sakhnik/arduin-o-punch/arduino/src/Operation.cpp

#include "Operation.h"
#include "Buzzer.h"
#include "Settings.h"
#include "Bluetooth.h"
#include "Network.h"
#include "CpuFreq.h"
#include "defs.h"
#include "ActivityCounter.h"
#include "RtcLog.h"
#include <SPI.h>
#include <esp_sleep.h>
#include <driver/gpio.h>
#include <RTClib.h>
#include <Preferences.h>

// Should always keep non-DST time
RTC_DS3231 rtc;

namespace {

Preferences prefs;

// Hold some pins in the high state during sleep to keep RFC522 and DS3231 switched off and to avoid parasitic current
static constexpr const int HIGH_PINS[] = {MOSFET_PIN, BUZZER_PIN};

constexpr const int TIME_TO_SLEEP_MS = 500;

constexpr const char *const PREF_STATS = "stats";
constexpr const char *const PREF_PREV_TRANSITION = "prev-trans";
constexpr const char *const PREF_PREV_MODE = "prev-mode";
constexpr const char *const PREF_TIMES = "times";

} //namespace;

Operation::Operation(Buzzer &buzzer, Settings &settings, OutMux &outMux, Bluetooth &bluetooth, Network &network)
    : buzzer{buzzer}
    , settings{settings}
    , bluetooth{bluetooth}
    , network{network}
    , puncher{settings, *this, buzzer, outMux}
{
}

int Operation::Setup()
{
    gpio_deep_sleep_hold_dis();
    for (int pin : HIGH_PINS) {
        gpio_hold_dis(static_cast<gpio_num_t>(pin));
    }

    pinMode(MOSFET_PIN, OUTPUT);
    pinMode(WAKEUP_PIN, INPUT_PULLUP);

    // Power on the RFID reader
    digitalWrite(MOSFET_PIN, LOW);

    Wire.setPins(I2C_SDA, I2C_SCL);
    if (!rtc.begin()) {
        Serial.println("Couldn't find RTC");
        Serial.flush();
        buzzer.SignalRTCFail();
        return -1;
    }

    if (puncher.Setup())
        return -1;

    if (RtcLog::IsReliable()) {
        // Restore the previous mode to preserve the accurate statistics
        prefs.begin(PREF_STATS, true);
        prevTransitionTime = prefs.getULong(PREF_PREV_TRANSITION, rtc.now().unixtime());
        auto prevMode = prefs.getInt(PREF_PREV_MODE, static_cast<int>(Mode::Sleep));
        if (prevMode < static_cast<int>(Mode::Count)) {
            mode = static_cast<Mode>(prevMode);
        }
        prefs.getBytes(PREF_TIMES, timeStats.data(), sizeof(timeStats));
        prefs.end();
    } else {
        prevTransitionTime = rtc.now().unixtime();
    }

    prevCardTimeMs = millis();
    return 0;
}

void Operation::SetupLate()
{
    if (!settings.IsKeyDefault()) {
        // Set the CPU frequency to 10 MHz for power optimization
        setCpuFrequencyMhz(10);
        Serial.print(F("CPU Frequency: "));
        Serial.print(getCpuFrequencyMhz());
        Serial.println(F(" MHz"));

        // Transition to the default mode and record the time in the sleep/previous mode
        TransitionTo(Mode::Eco, /*silent=*/true);
    } else {
        TransitionTo(Mode::Active, /*silent=*/true);
    }

    // Stay up for at least some time
    EnsureSmallAwake(true);
}

void Operation::EnsureSmallAwake(bool force)
{
    constexpr uint32_t SMALL_AWAKE_MS = 10'000;

    auto now = millis();
    if (force || now - prevCardTimeMs < SMALL_AWAKE_MS) {
        prevCardTimeMs = millis() + SMALL_AWAKE_MS - settings.GetEcoMs();
    }

}

void Operation::Loop()
{
    for (int i = 0; i < 2; ++i) {
        auto res = puncher.Punch();
        if (!res) {
            TransitionToActive();
            buzzer.ConfirmPunch();
        } /*else {
            if (res == ErrorCode::NO_CARD) {
                Serial.print('.');
            } else {
                Serial.println((int)res);
            }
            Serial.flush();
        }*/

        if (res == ErrorCode::CARD_IS_FULL) {
            TransitionToActive();
            buzzer.SignalCardFull();
        } else if (res == ErrorCode::SERVICE_CARD) {
            TransitionToNext();
            EnsureSmallAwake();
        } else if (res == ErrorCode::DEBUG_CARD) {
            buzzer.ConfirmDebug();
        }
    }

    if (CheckSnooze()) {
        puncher.Setup();
    }
}

Operation::Mode Operation::GetNextMode()
{
    switch (mode) {
    case Mode::Active:
    case Mode::Eco:
        return Mode::BLE;
    case Mode::BLE:
#if defined(ENABLE_WIFI) && ENABLE_WIFI
        return Mode::WiFi;
    case Mode::WiFi:
#endif
        return Mode::Eco;
    default:
        break;
    }
    return Mode::Eco;
}

void Operation::TransitionTo(Mode nextMode, bool silent)
{
    switch (mode) {
    case Mode::Active:
    case Mode::Eco:
        break;
    case Mode::BLE:
        bluetooth.SwitchOff();
        break;
#if defined(ENABLE_WIFI) && ENABLE_WIFI
    case Mode::WiFi:
        network.SwitchOff();
        break;
#endif
    default:
        break;
    }

    // Record the time spent in the previous mode
    auto now = rtc.now().unixtime();
    {
        LockGuard lock{mutex};
        timeStats[static_cast<size_t>(mode)] += now - prevTransitionTime;
        prevTransitionTime = now;
        prefs.begin(PREF_STATS, false);
        prefs.putULong(PREF_PREV_TRANSITION, now);
        prefs.putInt(PREF_PREV_MODE, static_cast<int>(nextMode));
        prefs.end();
    }

    mode = nextMode;

    switch (mode) {
    case Mode::Active:
    case Mode::Eco:
        SetCpuFreq(10);
        if (!silent) {
            buzzer.SignalOk();
        }
        break;
    case Mode::BLE:
        SetCpuFreq(80);
        if (!silent) {
            buzzer.SignalBluetooth();
        }
        bluetooth.SwitchOn();
        break;
#if defined(ENABLE_WIFI) && ENABLE_WIFI
    case Mode::WiFi:
        SetCpuFreq(80);
        // It takes a second or so to initialize WiFi. The CPU will be busy.
        // Play a confirmation melody only after that to avoid distortion.
        network.SwitchOn();
        if (!silent) {
            buzzer.SignalWifi();
        }
        break;
#endif
    case Mode::Sleep:
        EnterSleep();
        break;
    default:
        // Shouldn't be reached
        break;
    }
}

void Operation::EnterSleep()
{
    prefs.begin(PREF_STATS, false);
    prefs.putULong(PREF_PREV_TRANSITION, prevTransitionTime);
    prefs.putBytes(PREF_TIMES, timeStats.data(), sizeof(timeStats));
    prefs.end();

    esp_sleep_disable_wakeup_source(ESP_SLEEP_WAKEUP_TIMER);
    esp_deep_sleep_enable_gpio_wakeup(1ULL << WAKEUP_PIN, ESP_GPIO_WAKEUP_GPIO_LOW);

    // stop buses
    SPI.end();
    Wire.end();

    // Configure high impedance state for the I²C and SPI
    auto high_z = [](int pin) {
        gpio_set_direction((gpio_num_t)pin, GPIO_MODE_DISABLE);
        gpio_set_pull_mode((gpio_num_t)pin, GPIO_FLOATING);
    };

    high_z(SPI_MOSI);
    high_z(SPI_MISO);
    high_z(SPI_SCK);
    high_z(SPI_SS);
    high_z(I2C_SDA);
    high_z(I2C_SCL);

    for (int pin : HIGH_PINS) {
        pinMode(pin, OUTPUT);
        digitalWrite(pin, HIGH);
        gpio_hold_en(static_cast<gpio_num_t>(pin));
    }

    // Enable the pins hold
    gpio_deep_sleep_hold_en();

    delay(100);
    esp_deep_sleep_start();
    // Should never reach!
    prevCardTimeMs = millis();
}

void Operation::TransitionToActive()
{
    if (mode == Mode::Eco) {
        TransitionTo(Mode::Active, /*silent=*/true);
    }
    prevCardTimeMs = millis();
}

void Operation::TransitionToNext()
{
    TransitionTo(GetNextMode());
}

bool Operation::CheckSnooze()
{
    if (settings.IsKeyDefault()) {
        return false;
    }

    auto millisNow = millis();

    if (mode == Mode::BLE && bluetooth.GetInactivitySeconds() > 120) {
        TransitionTo(Mode::Eco);
        prevCardTimeMs = millisNow;
        return false;
    }

#if defined(ENABLE_WIFI) && ENABLE_WIFI
    if (mode == Mode::WiFi && network.GetInactivitySeconds() > 120) {
        TransitionTo(Mode::Eco);
        prevCardTimeMs = millisNow;
        return false;
    }
#endif

    if (mode == Mode::Eco && millisNow - prevCardTimeMs >= settings.GetEcoMs()) {
        TransitionTo(Mode::Sleep);
        // Never reached
        return false;
    }

    if (mode == Mode::Active && millisNow - prevCardTimeMs >= settings.GetActiveMs()) {
        TransitionTo(Mode::Eco, /*silent=*/true);
        prevCardTimeMs = millisNow;
        return false;
    }

    if (mode == Mode::Eco && !ActivityCounter::Instance().IsBusy()) {
        digitalWrite(MOSFET_PIN, HIGH);
        //Serial.flush();
        esp_sleep_enable_timer_wakeup(TIME_TO_SLEEP_MS * 1000ull);
        esp_light_sleep_start();
        digitalWrite(MOSFET_PIN, LOW);
        vTaskDelay(pdMS_TO_TICKS(50));
        // Did snooze, need to reset the puncher
        return true;
    }

    return false;
}

void Operation::ResetStats()
{
    LockGuard lock{mutex};
    prevTransitionTime = rtc.now().unixtime();
    timeStats.fill(0);
}

Stats Operation::GetStats()
{
    Stats stats;
    stats.bootCount = RtcLog::bootCount;
    stats.lastResetReason = RtcLog::lastReset;

    auto now = rtc.now().unixtime();
    {
        LockGuard lock{mutex};
        for (int i = 0; i < static_cast<int>(OperationMode::Count); ++i) {
            stats.timeStats[i] = timeStats[i];
        }
        // Account the ongoing mode
        stats.timeStats[static_cast<size_t>(mode)] += now - prevTransitionTime;
        for (int i = 0; i < static_cast<int>(OperationMode::Count); ++i) {
            stats.timeStats[i] = timeStats[i];
        }
    }

    return stats;
}
