sakhnik/arduin-o-punch/arduino/src/Operation.h

#pragma once

#include "Mutex.h"
#include "OperationMode.h"
#include "Stats.h"
#include "Puncher.h"
#include <array>

class Buzzer;
class Bluetooth;
class Network;
class Settings;

class Operation
{
public:
    Operation(Buzzer &, Settings &, OutMux &, Bluetooth &, Network &);

    int Setup();
    void SetupLate();
    void Loop();

    void TransitionToActive();
    void TransitionToNext();
    bool CheckSnooze();

    void ResetStats();
    Stats GetStats();

private:
    Buzzer &buzzer;
    Settings &settings;
    Bluetooth &bluetooth;
    Network &network;
    Puncher puncher;
    // Start in the sleep mode to record the sleep time
    using Mode = OperationMode;
    Mode mode = Mode::Sleep;
    Mutex mutex;
    uint32_t prevCardTimeMs = 0;
    uint32_t prevTransitionTime = 0;
    using StatsT = std::array<uint32_t, static_cast<size_t>(Mode::Count)>;
    StatsT timeStats = {};

    void TransitionTo(OperationMode, bool silent = false);
    OperationMode GetNextMode();
    void EnterSleep();
    void EnsureSmallAwake(bool force = false);
};
