sakhnik/arduin-o-punch/arduino/src/Settings.h

#pragma once

#include "Recorder.h"
#include "Mutex.h"
#include "PunchCard.h"

#include <RTClib.h>
#include <array>
#include <functional>
#include <string_view>

class Buzzer;

class Settings
{
public:
    Settings(Buzzer &buzzer);

    Buzzer& GetBuzzer() const { return *_buzzer; }

    int8_t Setup();

    static constexpr const size_t KEY_SIZE = 6;
    using KeyT = AOP::IMifare::KeyT;
    KeyT GetKey();
    void SetKey(const KeyT &key);
    bool IsKeyDefault();

    using KeysT = AOP::PunchCard::KeysT;
    const KeysT& GetKnownKeys();
    void SetKnownKeys(KeysT &&);

    DateTime GetDateTime() const;
    uint32_t GetClock(const DateTime *date_time) const;
    void SetClock(uint32_t clock);
    void SetDateTime(uint32_t timestamp);

    uint8_t GetId();
    void SetId(uint8_t id);

    // Active polling time before going to the light sleep eco mode
    uint32_t GetActiveMinutes();
    void SetActiveMinutes(uint32_t minutes);
    uint32_t GetActiveMs();

    // Polling with light sleep before going to the deep sleep
    uint32_t GetEcoMinutes();
    void SetEcoMinutes(uint32_t minutes);
    uint32_t GetEcoMs();

    AOP::Recorder& GetRecorder() { return _recorder; }

#if defined(ENABLE_WIFI) && ENABLE_WIFI
    std::string GetWifiSsid();
    void SetWifiSsid(std::string_view ssid);

    std::string GetWifiPass();
    void SetWifiPass(std::string_view pass);
#endif

    using OnChangeT = std::function<void(void)>;
    size_t Subscribe(OnChangeT);
    void Unsubscribe(size_t);

    enum class CardMode
    {
        Punch,
        ReadOut,
        Format,
    };

    CardMode GetActiveCardMode() { return _cardMode; }
    const std::string& GetCardModeArg() const { return _cardModeArg; }

    void ActivateCardPunchMode() { _cardMode = CardMode::Punch; }
    void ActivateCardReadOutMode(std::string_view arg);
    void ActivateCardFormatMode(std::string_view arg);

private:
    Buzzer *_buzzer;
    Mutex _watchersMx;
    std::array<OnChangeT, 4> watchers = {};

    Mutex _dataMx;
    uint8_t _id = 1;
    KeyT _key = { 0xff, 0xff, 0xff, 0xff, 0xff, 0xff };
    KeysT _knownKeys;

    static constexpr const uint16_t DEFAULT_ACTIVE_MINUTES = 10;
    uint16_t _active_minutes = DEFAULT_ACTIVE_MINUTES;
    uint32_t _active_ms = 60000ul * _active_minutes;
    static constexpr const uint16_t DEFAULT_ECO_MINUTES = 3 * 60;
    uint16_t _eco_minutes = DEFAULT_ECO_MINUTES;
    uint32_t _eco_ms = 60000ul * _eco_minutes;

#if defined(ENABLE_WIFI) && ENABLE_WIFI
    std::string _wifi_ssid;
    std::string _wifi_pass;
#endif

    AOP::Recorder _recorder;

    CardMode _cardMode = CardMode::Punch;
    std::string _cardModeArg;

    void NotifyWatchers();

    friend struct RecorderAccess;
};
