sakhnik/arduin-o-punch/arduino/src/Shell.h

#pragma once

#include <Arduino.h>
#include <freertos/FreeRTOS.h>
#include <freertos/queue.h>
#include <freertos/task.h>

class Settings;
class Buzzer;
class Operation;
class DateTime;
class OutMux;

class Shell
{
public:
    Shell(OutMux &, Settings &, Buzzer &);

    void Setup();
    void SetOperation(Operation *);

    void ProcessInput(const uint8_t *data, int size);
    void PutChar(char ch);

    void SetId(const char *str);
    void SetActive(const char *str);
    void SetEco(const char *str);
    void SetKey(const char *hex);

private:
    OutMux &_outMux;
    Settings &_settings;
    Buzzer &_buzzer;
    Operation *_operation = nullptr;

    QueueHandle_t _rxQueue;

    static void TaskEntry(void *arg);
    void _Task();

    void _PrintPrompt();
    void _Process(const String &);
    void _PrintId();
    void _PrintActive();
    void _PrintEco();
    void _PrintKey();
    void _SetClock(const char *str);
    void _PrintClock(const DateTime &time);
    void _SetTimestamp(const char *str);
    void _PrintTimestamp();
    void _PrintDate(const DateTime &time);
    void _PrintTime(const DateTime &time);
    void _RecorderCheck(const char *str);
    void _RecorderList();
    void _PrintDD(uint8_t d);
#if defined(ENABLE_WIFI) && ENABLE_WIFI
    void _SetWifiSsid(const char *str);
    void _PrintWifiSsid();
    void _SetWifiPass(const char *str);
    void _PrintWifiPass();
#endif
    void _PrintKnownKeys();
    void _SetKnownKeys(const char *str);
};
