sakhnik/arduin-o-punch/arduino/src/Bluetooth.h

#pragma once

#include "OutMux.h"
#include "RingBuffer.h"
#include "Mutex.h"
#include <freertos/FreeRTOS.h>
#include <freertos/semphr.h>
#include <atomic>

class Settings;
class Shell;

class Bluetooth
    : private OutMux::IClient
{
public:
    Bluetooth(OutMux &, Settings &, Shell &);

    void Setup();
    void SwitchOn();
    void SwitchOff();
    unsigned GetInactivitySeconds();

private:
    OutMux &_outMux;
    Settings &_settings;
    Shell &_shell;
    std::atomic<bool> _stopRequested{false};
    AOP::RingBuffer<1024> _outBuffer;
    std::atomic<unsigned long> _lastStdinTimeMs = 0;
    Mutex _txMutex;
    SemaphoreHandle_t _txSignal = nullptr;
    TaskHandle_t _taskHandle = nullptr;
    size_t _subscription_handle = -1;

    static void _TaskEntry(void *arg);
    void _Task();
    bool _Start();
    bool _Stop();

    // MuxOut::IClient
    void Write(const uint8_t *buffer, size_t size) override;
};
